WeSpeakEnglish/LoRa-E5_weather_and_pollution/Core/Inc/nortos.h

/*
 * nortos.h
 *
 *  Created on: Sep 3, 2022
 *      Author: pinelab
 */

#ifndef INC_NORTOS_H_
#define INC_NORTOS_H_



extern void F1_QueueIni(void); // initialization of Queue
extern int F1_push(void (*pointerQ)(void) ); // push element into the queue
extern void (*F1_pull(void))(void); // pull element from the queue

// ------ 8<----8<----8<----8<----8<----8<----8<----8<----8<----8<----8<----8<----8<----8<----8<----8<----8<----8<----8<----8<----8<----
extern void F2_QueueIni(void); // initialization of Queue
extern int F2_push(void (*pointerQ)(void) ); // push element into the queue
extern void (*F2_pull(void))(void); // pull element from the queue


#endif /* INC_NORTOS_H_ */
