WeSpeakEnglish/LoRa-E5_weather_and_pollution/Core/Src/nortos.c

/*
 * nortos.c
 *
 *  Created on: Sep 3, 2022
 *      Author: pinelab
 */


#include "nortos.h"

#define Q_SIZE_FAST 16

volatile int F1_last; // number of last element of fast-speed queue
int F1_first; // number of first element of fast-speed queue

void SimpleF1(){;};

void (*F1_Queue[Q_SIZE_FAST])();

 void F1_QueueIni(void){ // initialization of Queue
  F1_last = 0;
  F1_first = 0;
}

 int F1_push(void (*pointerQ)(void) ){ // push element from the queue
  if ((F1_last+1)%Q_SIZE_FAST == F1_first)return 1;
  F1_Queue[F1_last++] = pointerQ;
  F1_last%=Q_SIZE_FAST;
  return 0;
}

 void (*F1_pull(void))(void){ // pull element from the queue
  void (*pullVar)(void);
  if (F1_last == F1_first)return SimpleF1;
  pullVar = F1_Queue[F1_first++];
  F1_first%=Q_SIZE_FAST;
  return pullVar;
}
 // ------ 8<----8<----8<----8<----8<----8<----8<----8<----8<----8<----8<----8<----8<----8<----8<----8<----8<----8<----8<----8<----8<----

 volatile int F2_last; // number of last element of fast-speed queue
 int F2_first; // number of first element of fast-speed queue

 void SimpleF2(){;};

 void (*F2_Queue[Q_SIZE_FAST])();

 void F2_QueueIni(void){ // initialization of Queue
   F2_last = 0;
   F2_first = 0;
 }

 int F2_push(void (*pointerQ)(void) ){ // push element from the queue
   if ((F2_last+1)%Q_SIZE_FAST == F2_first)return 1;
   F2_Queue[F2_last++] = pointerQ;
   F2_last%=Q_SIZE_FAST;
   return 0;
 }

 void (*F2_pull(void))(void){ // pull element from the queue
   void (*pullVar)(void);
   if (F2_last == F2_first)return SimpleF2;
   pullVar = F2_Queue[F2_first++];
   F2_first%=Q_SIZE_FAST;
   return pullVar;
 }
